o7-machinehum/wifiwart/electronics/datasheets/pu.png

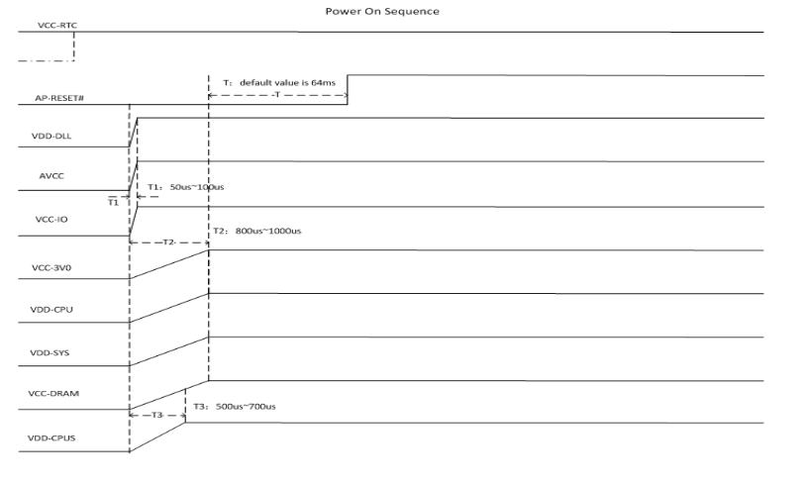
electronics/datasheets/pu.png
