o7-machinehum/wifiwart/electronics/nff_pcb/R0.1/pic/PXL_20210526_214039443.jpg

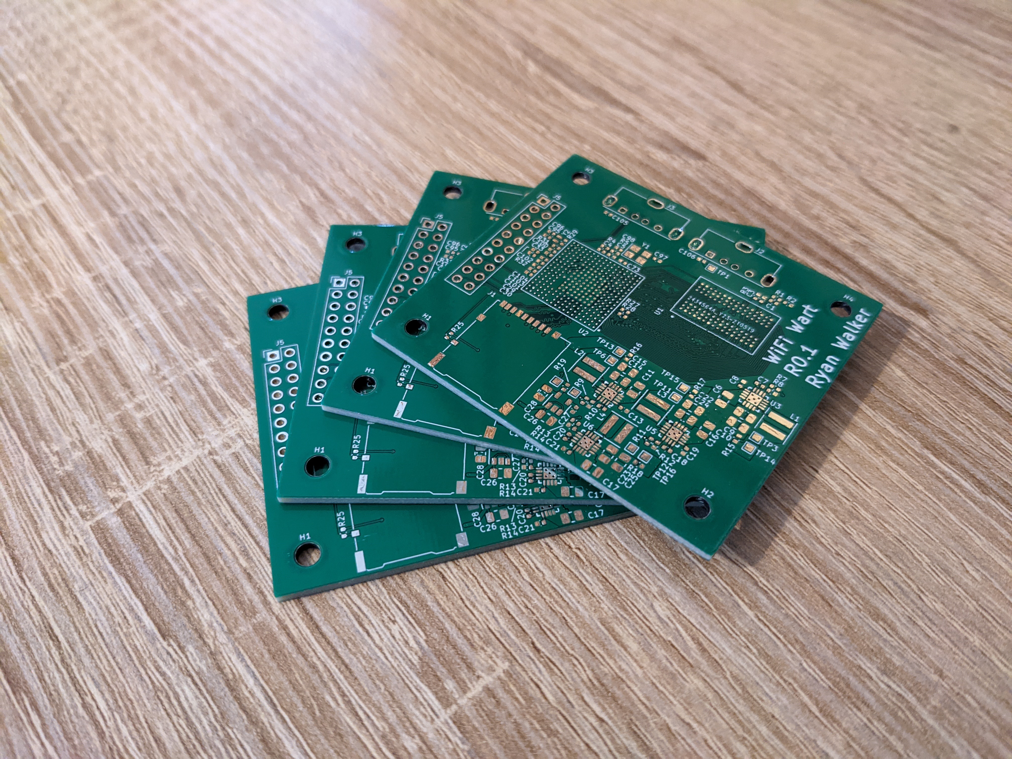
electronics/nff_pcb/R0.1/pic/PXL_20210526_214039443.jpg
