o7-machinehum/wifiwart/electronics/nff_pcb/R0.1/pic/PXL_20210526_214057652.jpg

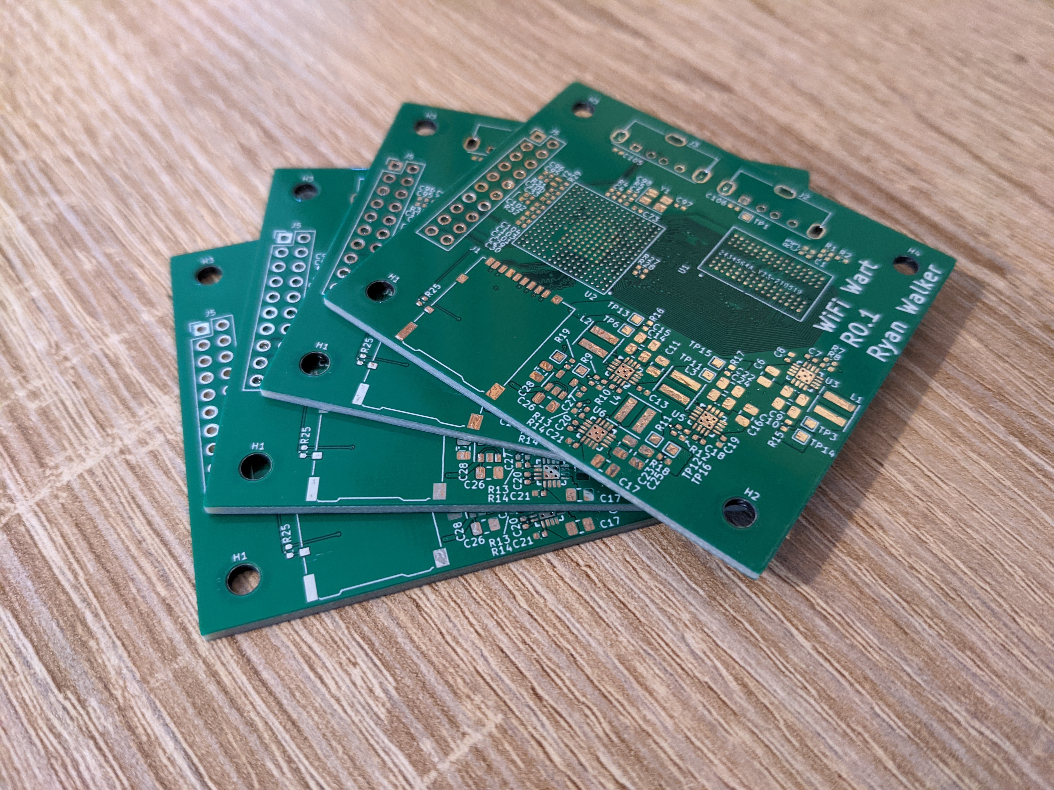
electronics/nff_pcb/R0.1/pic/PXL_20210526_214057652.jpg
