o7-machinehum/wifiwart/mech/refs/nema5-15.jpg

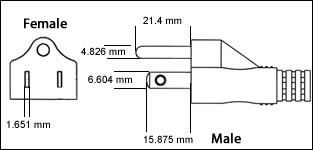
mech/refs/nema5-15.jpg
