o7-machinehum/wifiwart/mech/refs/nema5-15.png

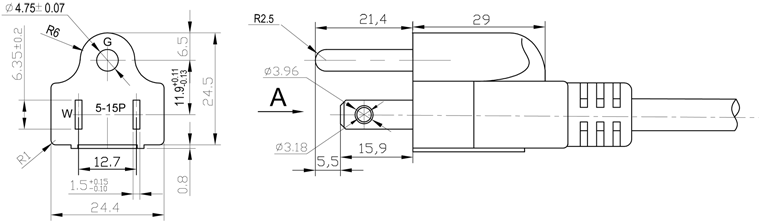
mech/refs/nema5-15.png
