o7-machinehum/wifiwart/media/complete/PXL_20211027_170327869.jpg

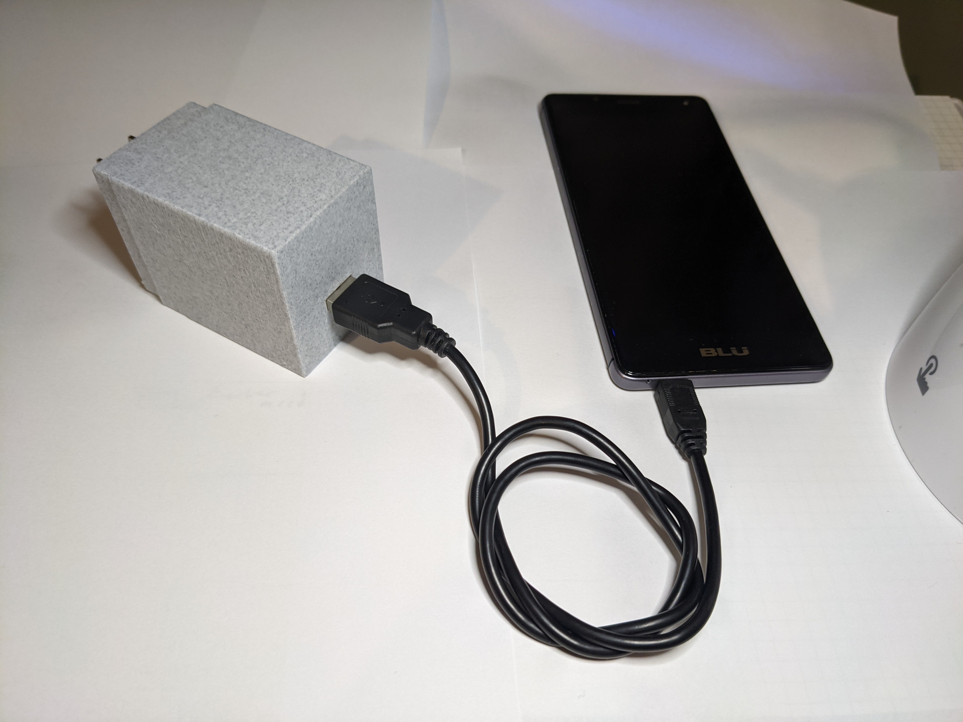
media/complete/PXL_20211027_170327869.jpg
