o7-machinehum/wifiwart/media/complete/PXL_20211027_170623045.jpg

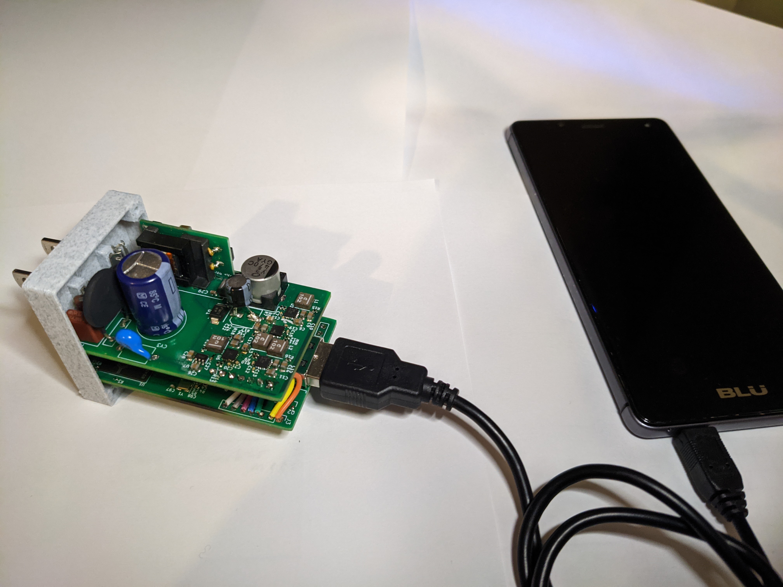
media/complete/PXL_20211027_170623045.jpg
