o7-machinehum/wifiwart/media/complete/PXL_20211027_170851948.jpg

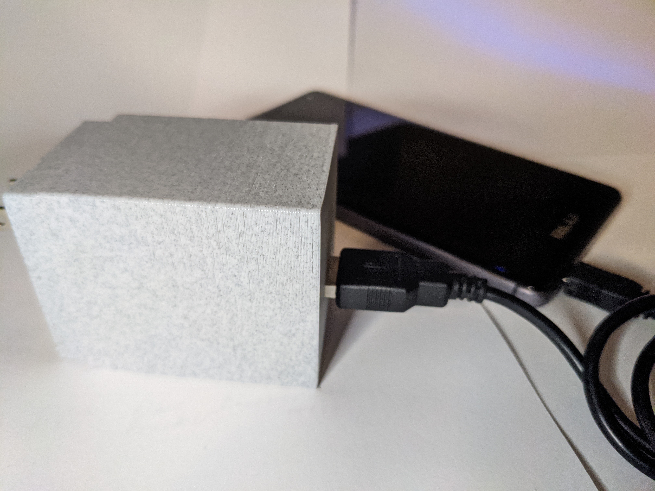
media/complete/PXL_20211027_170851948.jpg
