o7-machinehum/wifiwart/media/mech.png

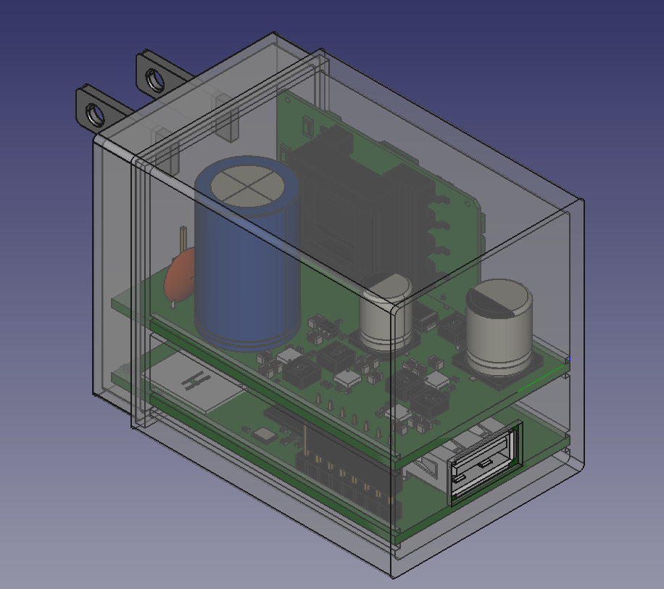
media/mech.png
