o7-machinehum/wifiwart/media/PXL_20210610_194850981.jpg

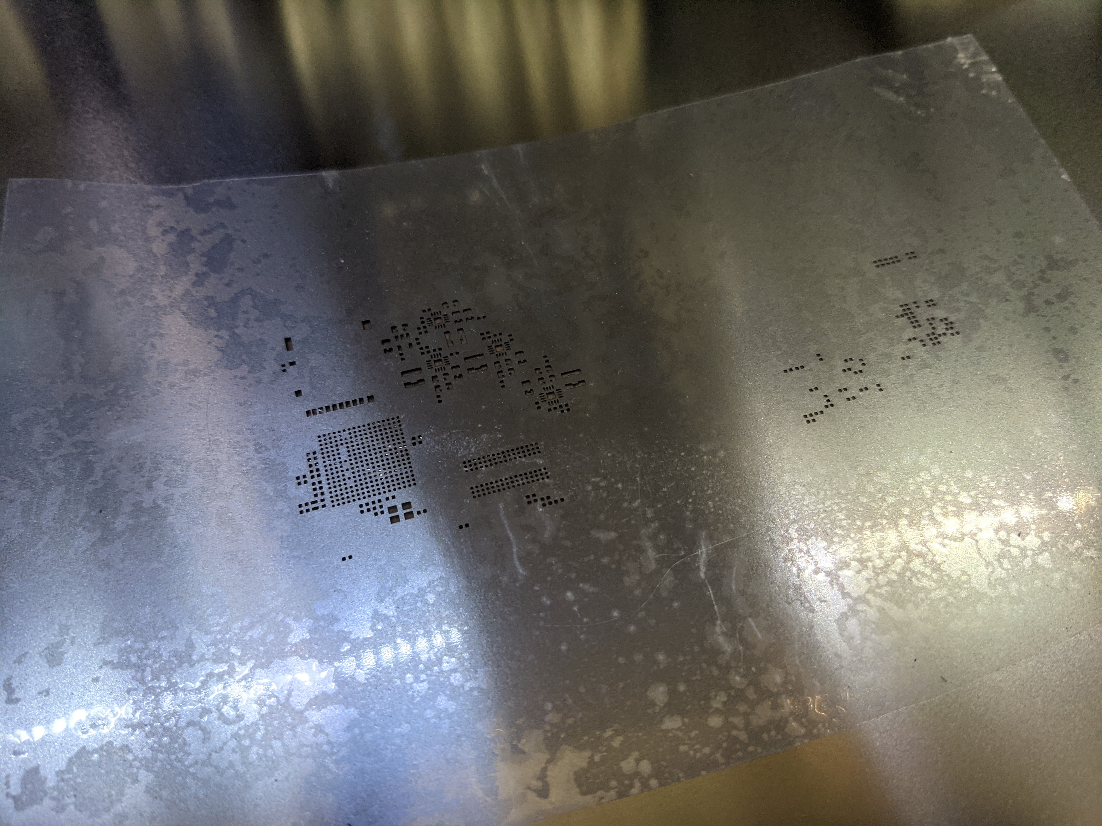
media/PXL_20210610_194850981.jpg
