o7-machinehum/wifiwart/media/PXL_20210610_195738112.jpg

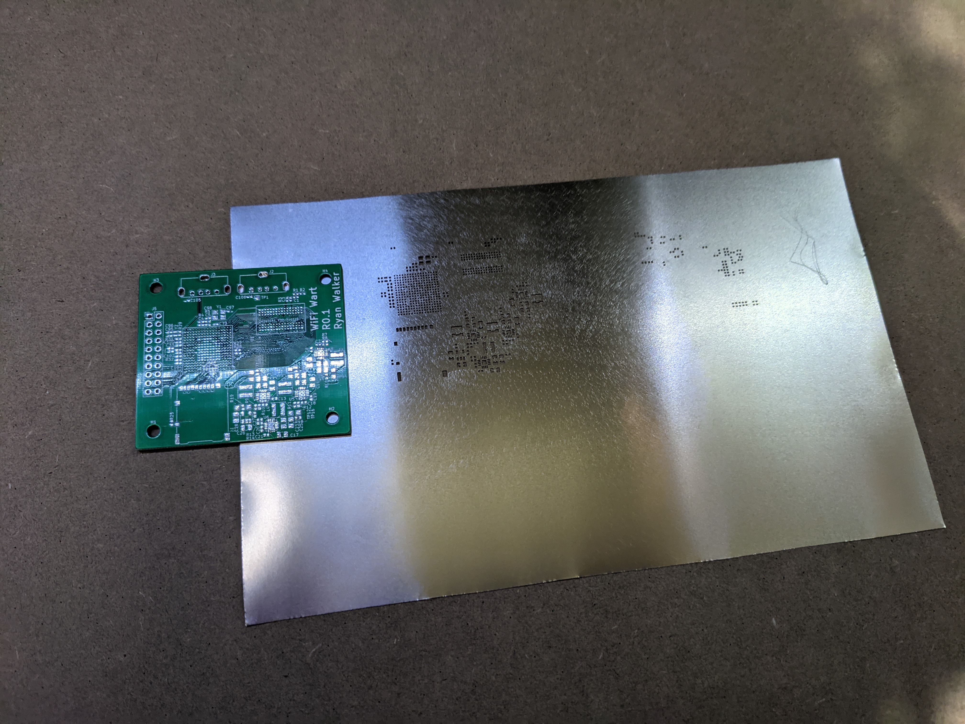
media/PXL_20210610_195738112.jpg
