o7-machinehum/wifiwart/media/PXL_20210610_201107477.jpg

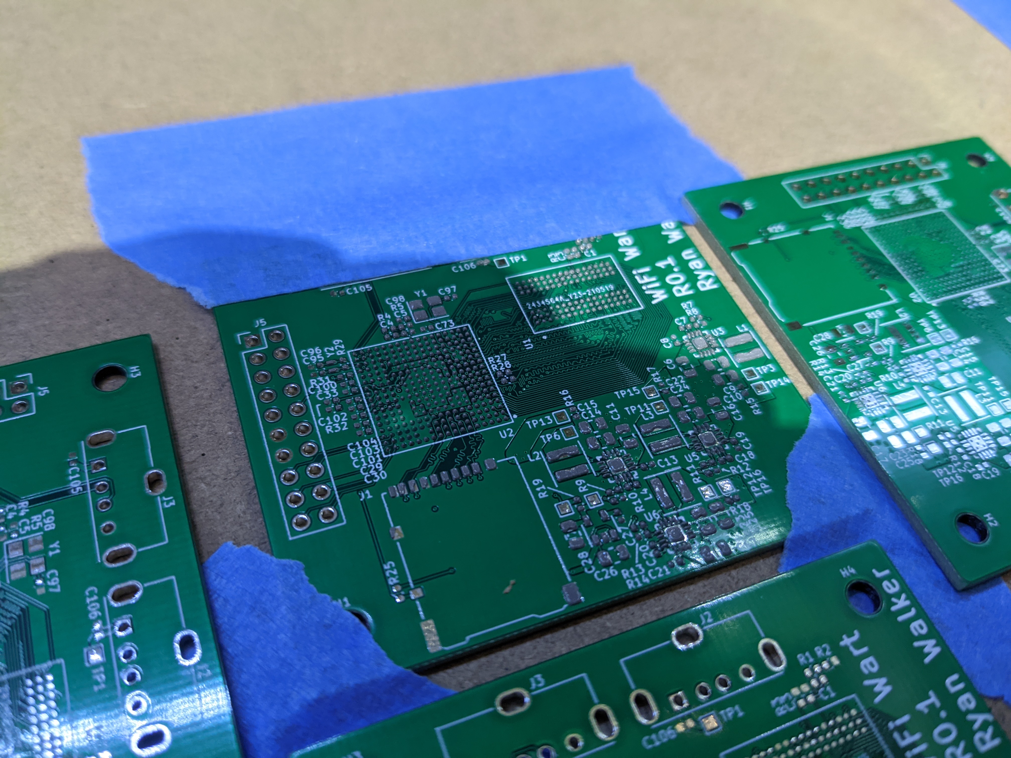
media/PXL_20210610_201107477.jpg
