o7-machinehum/wifiwart/media/PXL_20210610_202606074.jpg

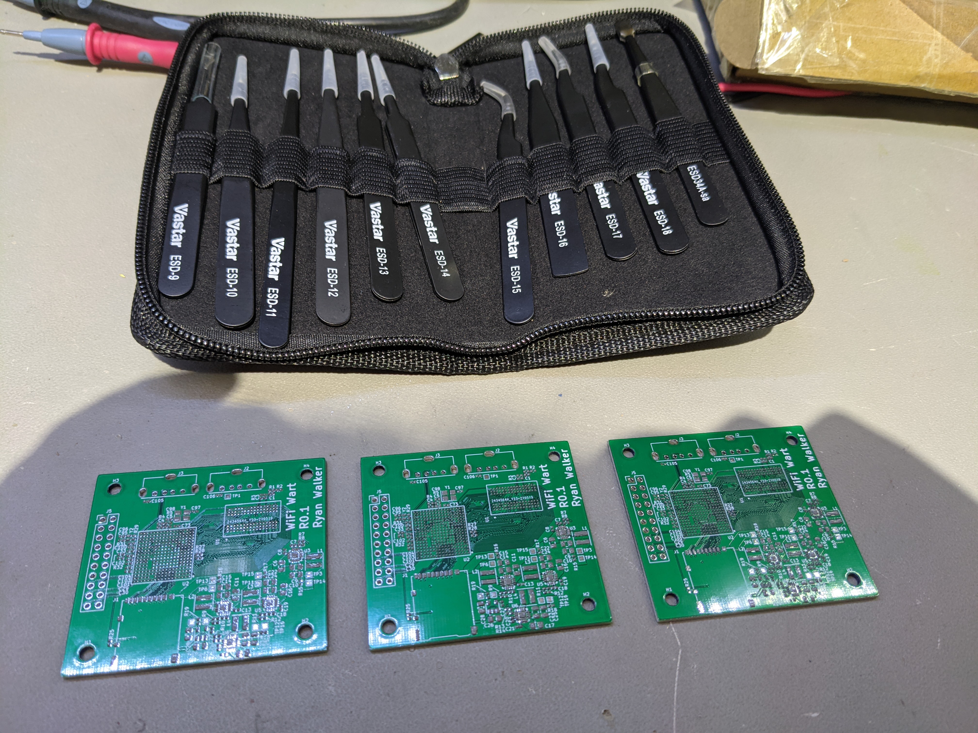
media/PXL_20210610_202606074.jpg
