o7-machinehum/wifiwart/media/PXL_20210611_000656087.jpg

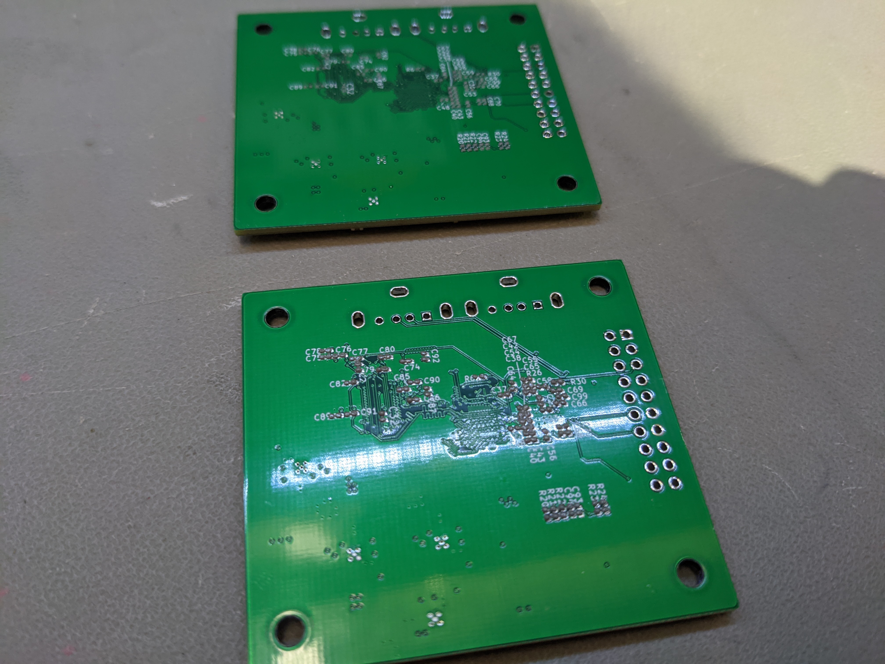
media/PXL_20210611_000656087.jpg
