o7-machinehum/wifiwart/media/PXL_20210611_012029887.jpg

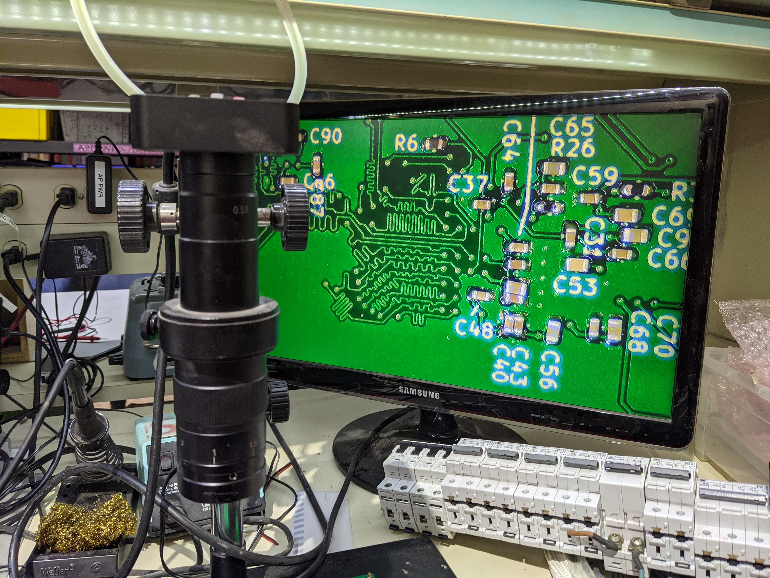
media/PXL_20210611_012029887.jpg
