o7-machinehum/wifiwart/media/PXL_20210611_012040361.jpg

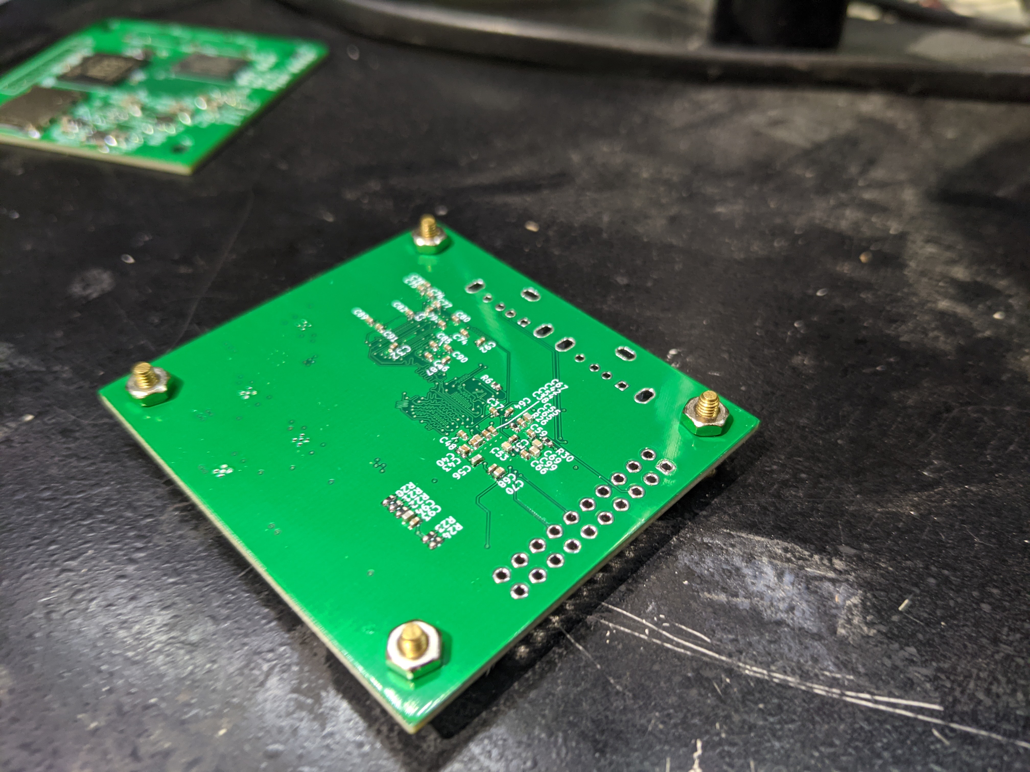
media/PXL_20210611_012040361.jpg
