o7-machinehum/wifiwart/electronics/ff_comp_pcb/step/QFN-3x3.step

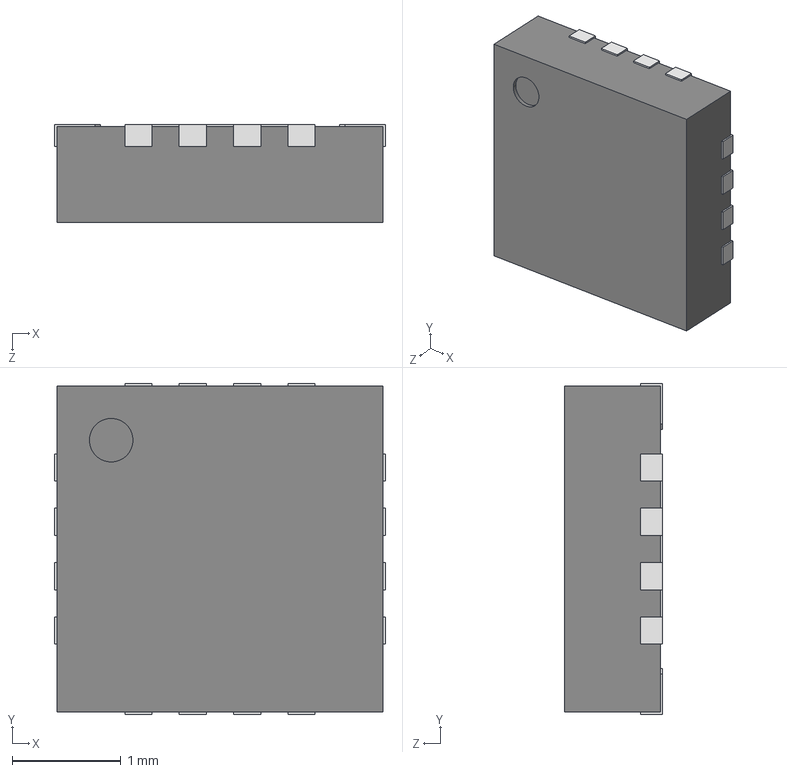
[picture p45: CAD file, 2021-04-29]
electronics/ff_comp_pcb/step/QFN-3x3.step
3.04 x 3.04 x 0.9 mm
ALSRobot-QFN16 3x3_User Library-QFN-16_3x3_1
ALSRobot-QFN16 3x3_User Library-QFN-16_3x3_2
ALSRobot-QFN16 3x3_User Library-QFN-16_3x3_3
ALSRobot-QFN16 3x3_User Library-QFN-16_3x3_4
ALSRobot-QFN16 3x3_User Library-QFN-16_3x3_5
ALSRobot-QFN16 3x3_User Library-QFN-16_3x3_6
ALSRobot-QFN16 3x3_User Library-QFN-16_3x3_7
ALSRobot-QFN16 3x3_User Library-QFN-16_3x3_8
ALSRobot-QFN16 3x3_User Library-QFN-16_3x3_9
ALSRobot-QFN16 3x3_User Library-QFN-16_3x3_10
ALSRobot-QFN16 3x3_User Library-QFN-16_3x3_11
ALSRobot-QFN16 3x3_User Library-QFN-16_3x3_12
ALSRobot-QFN16 3x3_User Library-QFN-16_3x3_13
ALSRobot-QFN16 3x3_User Library-QFN-16_3x3_14
ALSRobot-QFN16 3x3_User Library-QFN-16_3x3_15
ALSRobot-QFN16 3x3_User Library-QFN-16_3x3_16
ALSRobot-QFN16 3x3_User Library-QFN-16_3x3_17
ALSRobot-QFN16 3x3_User Library-QFN-16_3x3_18
