o7-machinehum/wifiwart/electronics/ff_power_pcb/Bourns/srr1208.stp

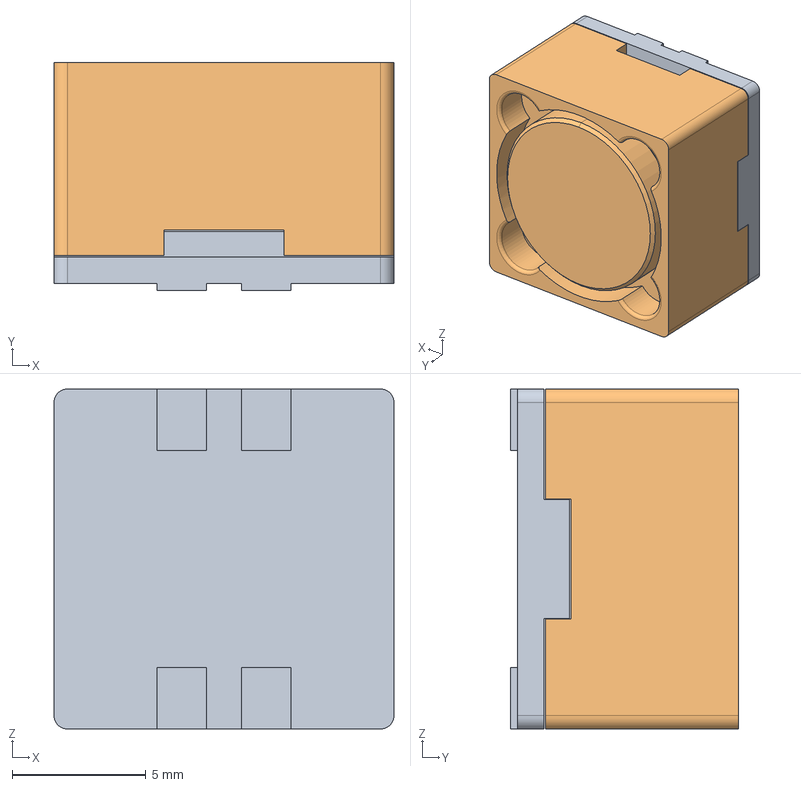
[picture p46: CAD file, 2021-06-07]
electronics/ff_power_pcb/Bourns/srr1208.stp
12.7 x 8.50 x 12.7 mm
