o7-machinehum/wifiwart/electronics/ff_power_pcb/step/Coilcraft-XAL4030.step

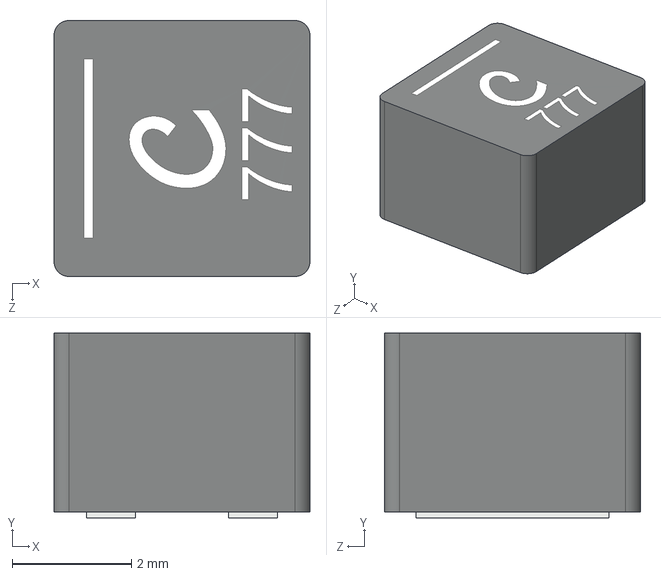
[picture p47: CAD file, 2021-08-04]
electronics/ff_power_pcb/step/Coilcraft-XAL4030.step
4.30 x 3.10 x 4.30 mm
