o7-machinehum/wifiwart/mech/out/prong-ModelParts.step

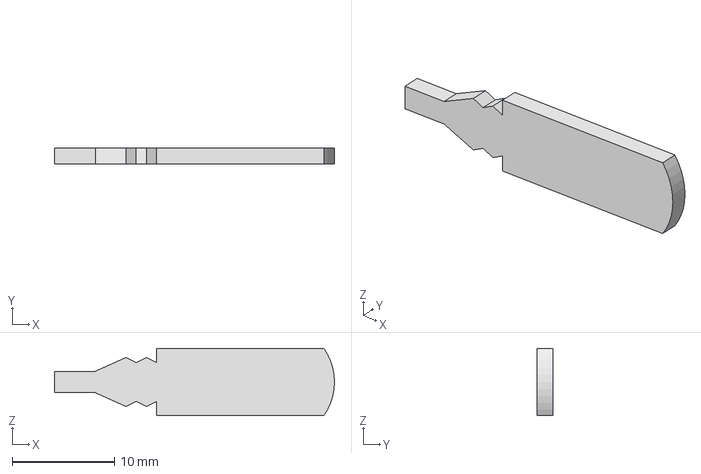
[picture p48: CAD file, 2021-08-07]
mech/out/prong-ModelParts.step
27.4 x 1.60 x 6.60 mm
