o7-machinehum/wifiwart/mech/prong.FCStd

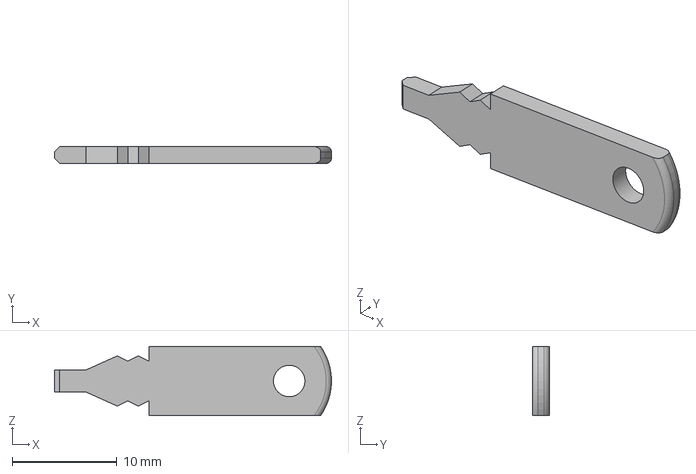
[picture p49: CAD file, 2021-10-17]
mech/prong.FCStd
26.4 x 1.60 x 6.60 mm
