o7-machinehum/wifiwart/electronics/ff_comp_pcb/step/DM3AT-SF-PEJM5.stp

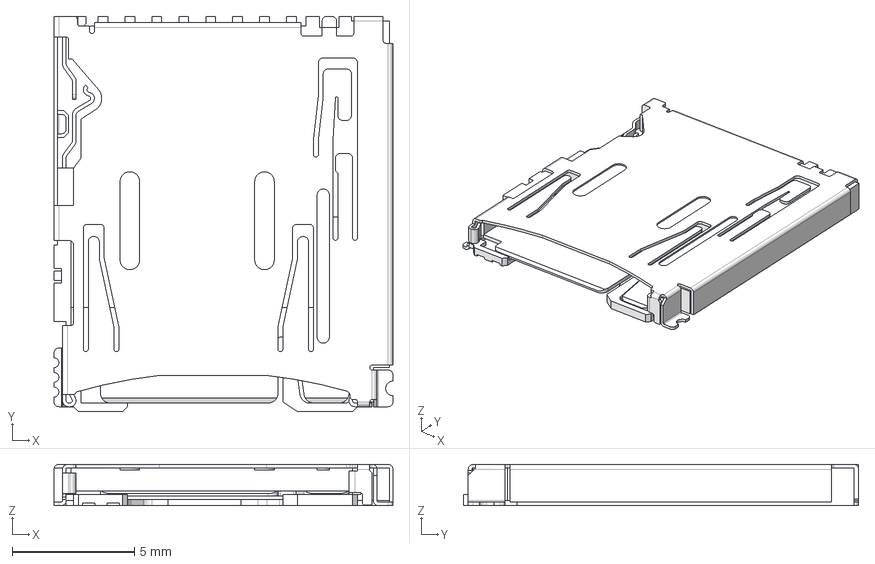
[picture p50: CAD file, 2021-03-17]
electronics/ff_comp_pcb/step/DM3AT-SF-PEJM5.stp
13.8 x 16.2 x 1.68 mm
