o7-machinehum/wifiwart/mech/comp_pcb.FCStd

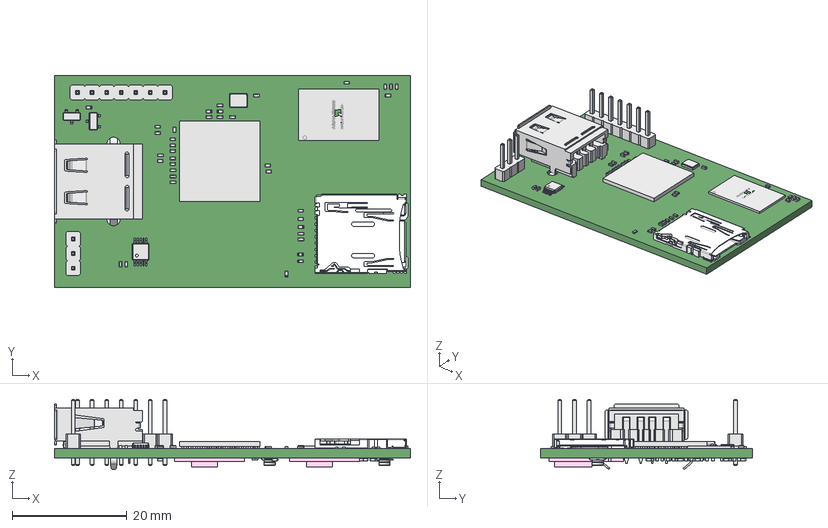
[picture p51: CAD file, 2021-09-03]
mech/comp_pcb.FCStd
62.0 x 37.0 x 12.2 mm
