o7-machinehum/wifiwart/mech/power_pcb.FCStd

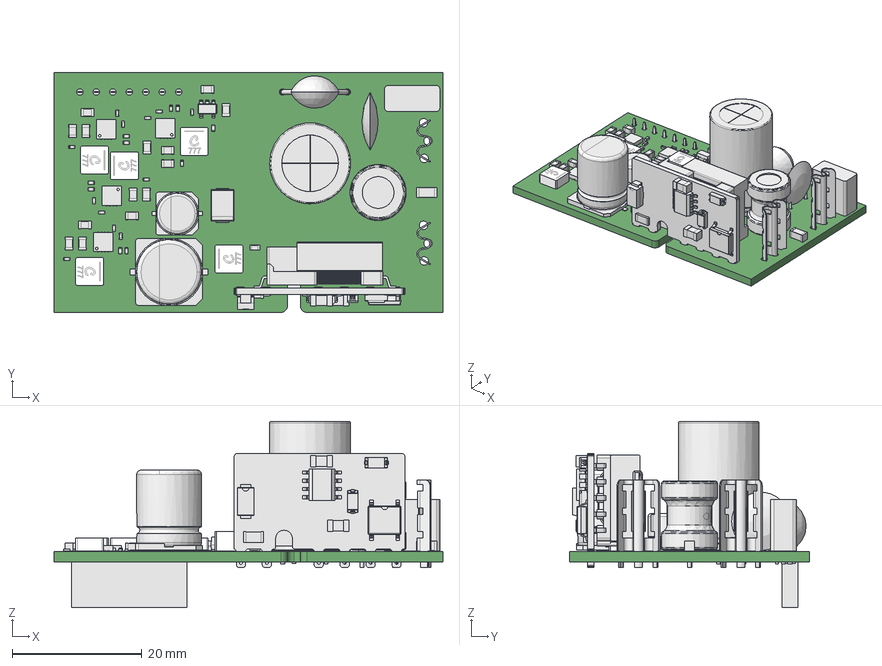
[picture p52: CAD file, 2021-09-03]
mech/power_pcb.FCStd
60.0 x 37.0 x 28.7 mm
