o7-machinehum/wifiwart/mech/patch_antenna.FCStd

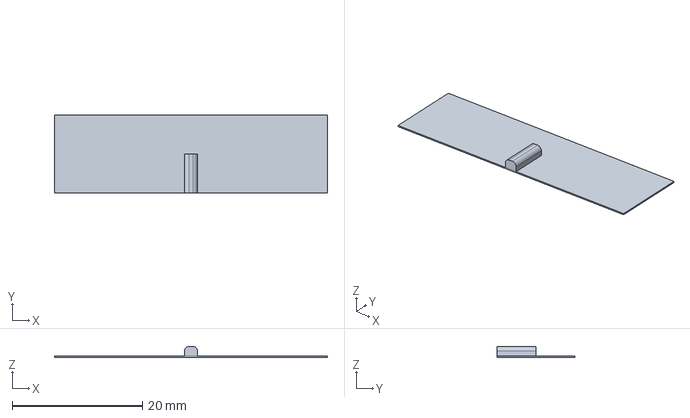
[picture p53: CAD file, 2021-06-10]
mech/patch_antenna.FCStd
42.0 x 12.0 x 1.70 mm
