o7-machinehum/wifiwart/media/PXL_20210610_194858042.jpg

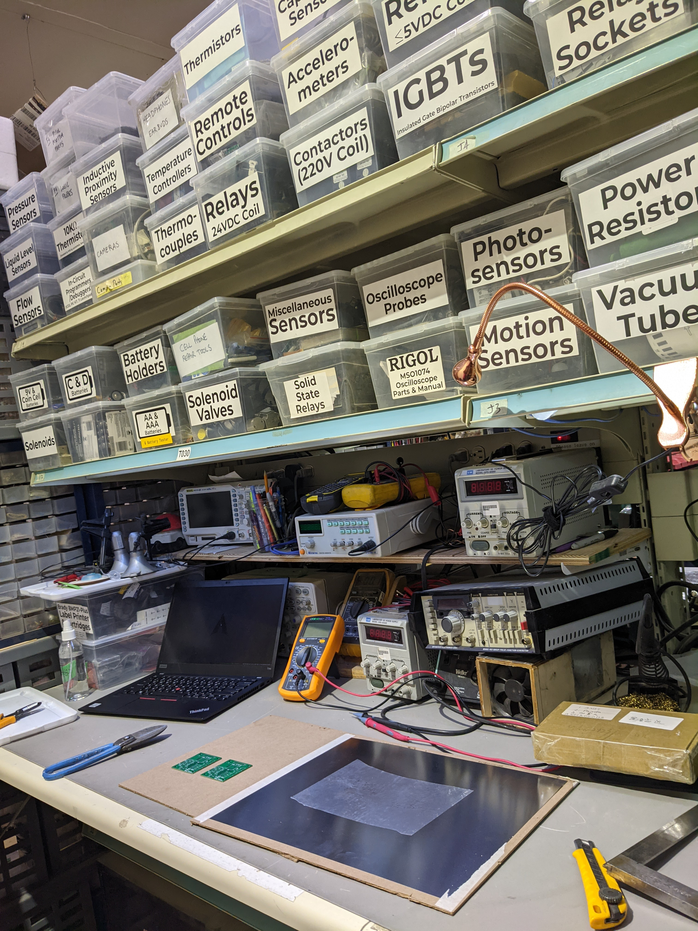
media/PXL_20210610_194858042.jpg
