o7-machinehum/wifiwart/media/PXL_20210610_200827033.MP.jpg

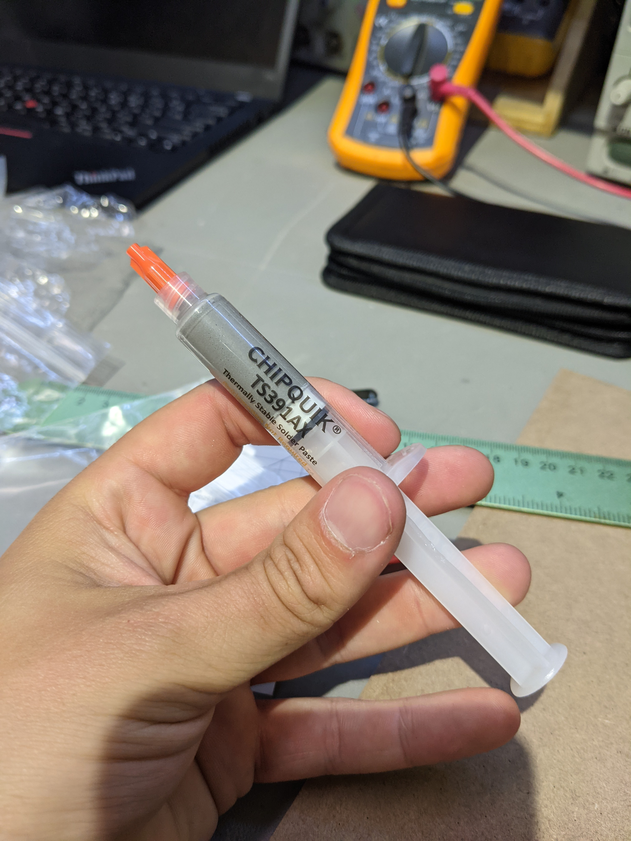
media/PXL_20210610_200827033.MP.jpg
