o7-machinehum/wifiwart/media/PXL_20210610_200916468.jpg

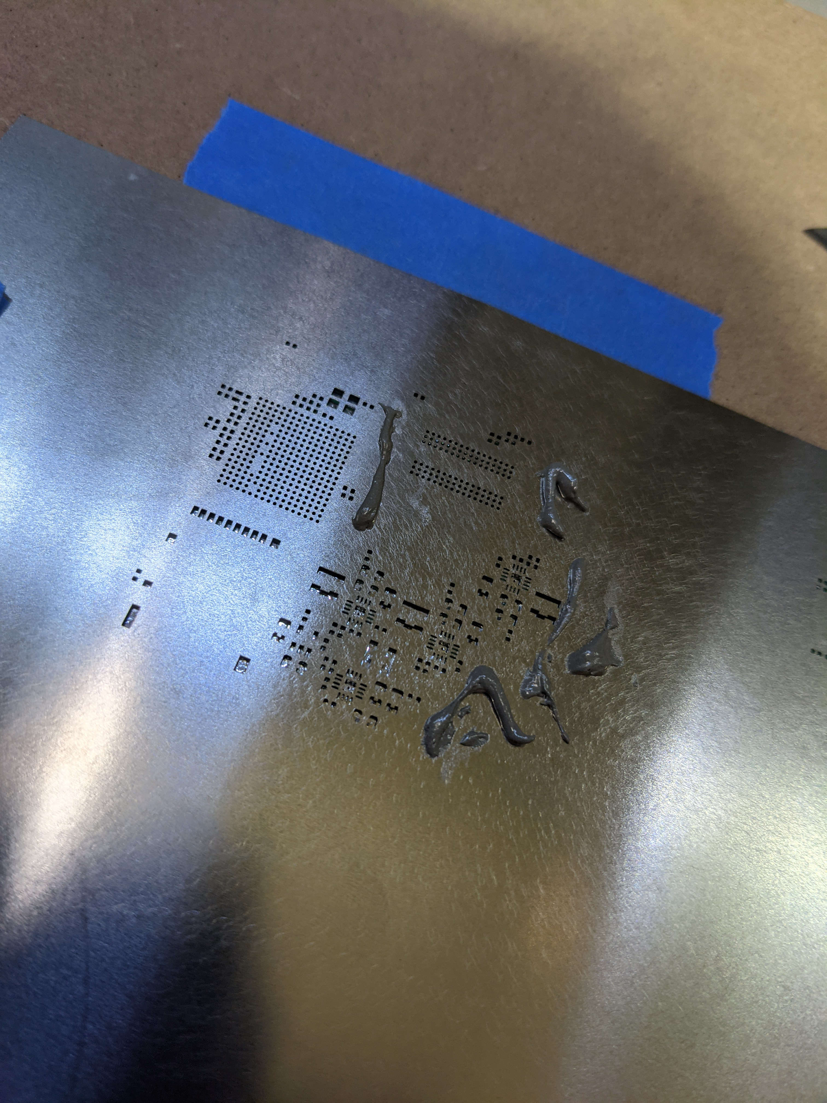
media/PXL_20210610_200916468.jpg
